davemuscle/10band_nixie/ltspice/AnalogStateVar_AC_DualSupply.asc

C1: cap; {CC}
C2: cap; {CC}
R1: res; {RR1}
R2: res; {RR2}
R3: res; {RR3}
R4: res; {RR}
R5: res; {RR}
R6: res; {RR6}
R7: res; {RR7}
R13: res; 10k
R14: res; 10k
U1: LT1632
U2: LT1632
U3: LT1632
V2: voltage; 2.5V
V3: voltage; -2.5V
V4: voltage; SINE(0 0.01 760); AC 1
Named nets: 0, V+, V-, Vbias, Vin, LP, BP, HP
.ac oct 24 20 20000
.param CC = 100n
.param RR1 = 10000
.param RR2 = 250
.param RR3 = 250
.param RR6 = 400k
.param RR = 2085
.param RR7 = 80k
