davemuscle/10band_nixie/ltspice/AnalogStateVar_AC_SingleSupply.asc

C1: cap; {CC}
C2: cap; {CC}
R1: res; {RR1}
R2: res; {RR2}
R3: res; {RR3}
R4: res; {RR_B1}
R5: res; {RR_B1}
R6: res; {RR7}
R7: res; {RR6}
R8: res; 10k
R9: res; 1k
U1: LT1632
U2: LT1632
U3: LT1632
U4: LT1632
V1: voltage; 2.5V
V2: voltage; 5V
V4: voltage; SINE(2.5V 0.1 760); AC 0.1
Named nets: 0, V+, Vin, V-, Vbias, Vgain, Vbp
.ac oct 24 20 20000
.param CC = 100n
.param RR1 = 10000
.param RR2 = 1k
.param RR3 = 1k
.param RR6 = 220k
.param RR_B1 = 2200
.param RR7 = 10k
;.tran 0 0.02 0.00 0.005
