davemuscle/10band_nixie/ltspice/ButterworthBandpass.asc

C1: cap; 100n
C2: cap; 100n
C3: cap; 100n
C4: cap; 100n
C5: cap; 100n
C6: cap; 100n
C7: cap; 100n
C8: cap; 100n
C9: cap; 100n
C10: cap; 100n
C11: cap; 100n
C12: cap; 100n
R1: res; 3.6k
R2: res; 2.5k
R3: res; 3.6k
R4: res; 500
R5: res; 300
R6: res; 300
R7: res; 500
R8: res; 4.3k
R9: res; 470
R10: res; 2.5k
R11: res; 3.3k
R12: res; 360
R13: res; 10k
R14: res; 10k
R15: res; 27k
R16: res; 22k
R17: res; 3k
R18: res; 330
R19: res; 2.2k
R20: res; 270
R21: res; 19k
R22: res; 15k
U1: LT1490
U2: LT1490
U3: LT1490
U4: LT1490
U5: LT1490
U6: LT1490
U7: LT1490
V1: voltage; -5V
V2: voltage; 5V
V4: voltage; SINE(2.5V 0.1 760); AC 0.1
Named nets: 0, V+, Vin, V-, Vbias
.ac oct 24 20 20000
;.tran 0 0.02 0.00 0.005
Lowpass is 440 Hz, Highpass is 630 Hz
Lowpass is 630 Hz, Highpass is 900 Hz (approx same Q as above)
