davemuscle/10band_nixie/ltspice/Chopper.asc

D1: diode; 1N914
D2: diode; 1N914
R1: res; 1k
V1: voltage; 1.8
V2: voltage; SINE(0 5 440)
Named nets: 0
.tran 0 0.01 0.00 0.005
