davemuscle/10band_nixie/ltspice/Doubler.asc

C1: polcap; 10µ
C2: polcap; 10µ
C3: polcap; 2.2µ
C4: polcap; 2.2µ
D1: diode; MURS120
D2: diode; MURS120
D3: diode; MURS120
D4: diode; MURS120
V1: voltage; PULSE(0 50 0 0 0 10us 20us)
V2: voltage; 50
Named nets: 0, Vin, Vdc
.tran 0 800u 0 1u
