davemuscle/10band_nixie/ltspice/FrontEnd.asc

C1: cap; 10µ
D1: diode
D2: diode
Q1: npn; 2N2222
Q2: npn; 2N2222
R1: res; {RR}
R2: res; {POT}
R3: res; {10.01k - POT}
R4: res; {POT}
R5: res; 500
R6: res; {RR}
R7: res; {RR}
R8: res; 500
R9: res; {RR}
R10: res; {RR}
R11: res; {RR}
R12: res; {RR}
R13: res; {RR}
R14: res; {RR}
R15: res; {2*RR}
R16: res; {2*RR}
R17: res; 1k
U1: LT1632
U2: LT1632
U3: LT1632
U4: LT1632
U5: LT1632
U6: LT1632
V1: voltage; 5V
V2: voltage; 2.5V
V3: voltage; SINE(0V 1 440 0 0 0 10)
Named nets: 0, V+, Vbias, Vin, Vpot, Vgain, Vatt
.tran 0 0.02 0.00 0.01
.param POT = 1
.param RR = 5k
