davemuscle/10band_nixie/ltspice/GaintoDB.asc

R1: res; 1k
R2: res; 1k
R3: res; 1k
R4: res; 1k
R5: res; 1k
R6: res; 1k
R7: res; 1k
R8: res; 1k
R9: res; 1k
R10: res; 1k
U1: LT1632
U2: LT1632
U3: LT1632
U4: LT1632
U5: LT1632
U6: LT1632
U7: LT1632
U8: LT1632
U9: LT1632
U10: LT1632
V1: voltage; 2.5
V2: voltage; 5
V3: voltage; 2.5V
V4: voltage; 2V
V5: voltage; 1.5V
V6: voltage; 1V
V7: voltage; 0.5V
V8: voltage; 0V
V9: voltage; 2.5V
V10: voltage; 3V
V11: voltage; 3.5V
V12: voltage; 4V
V13: voltage; 4.5V
Named nets: 0, Vbias, V+, Vgain
Potentiometer is 10K -> Vgain = 5V, gain = 6 dB
Potentiometer is 0K   -> Vgain = 0V, gain = -21 dB
.tran 0 10m 0 100u
