davemuscle/10band_nixie/ltspice/MFT.asc

C1: cap; {CC}
C2: cap; {CC}
C3: cap; {CC}
C4: cap; {CC}
R1: res; {RR3}
R2: res; {RR1}
R3: res; {RR2}
R4: res; {RR3}
R5: res; {RR1}
R6: res; {RR2}
U1: LT1632
U2: LT1632
V1: voltage; 5V
V2: voltage; 2.5V
V3: voltage; SINE(2.5V 100m 1.7k); AC 0.1
Named nets: 0, Vbias, V+, Vin
.param RR1 = 3905
.param RR2 = 7800
.param CC = 100n
.ac oct 20 20 20k
;.tran 0 0.025 0.00 0.05
.param RR3 = 240
