davemuscle/10band_nixie/ltspice/PeakDetect.asc

C1: cap; 10µ
C2: cap; 10µ
C3: cap; 1µ
C4: cap; 10µ
C5: cap; 10µ
C6: cap; 10µ
D1: diode; 1N4148
D2: diode; 1N4148
D3: diode; 1N4148
R1: res; 10k
R2: res; 100
R3: res; 10k
R4: res; 100
R5: res; 100k
R6: res; 10k
R7: res; 10k
R8: res; 10k
R9: res; 100
U1: LT1632
U2: LT1632
U3: LT1632
U4: LT1632
U5: LT1632
U6: LT1632
V1: voltage; 5V
V2: voltage; SINE(2.5V 0.5 120 0 0 0 20)
V3: voltage; -5V
V4: voltage; 2.5V
Named nets: 0, VIN, VCC, VSS, Vin, Vbias
.tran 0 1 0.00 0.005
