davemuscle/10band_nixie/ltspice/PeakDetectorForCompressor.asc

C1: cap; 10µ
C2: cap; 1µ
D1: diode; 1N914
D2: diode; 1N914
D3: diode; 1N914
Q1: npn; 2N2222
Q2: npn; 2N2222
R1: res; 10k
R2: res; 1k
R3: res; 100
R4: res; 620k
R5: res; 100
R6: res; 1k
U1: LT1632
U2: LT1632
V1: voltage; SINE(0 5 440)
V2: voltage; 5V
V3: voltage; 2.5V
Named nets: 0, Input, V+, Vbias
.tran 0 0.01 0.00 0.05
