davemuscle/10band_nixie/ltspice/SallenKeyButterworthBandpass.asc

C1: cap; 100n
C2: cap; 100n
C3: cap; 100n
C4: cap; 100n
R1: res; 1.1k
R2: res; 1.1k
R3: res; 2.2k
R4: res; 2.2k
U1: LT1490
U2: LT1490
U3: LT1490
V1: voltage; SINE(0 0.1 440); AC 0.1
V2: voltage; 5V
V3: voltage; -5V
Named nets: 0, Vin, 5V, -5V
.ac oct 50 20 20k
