davemuscle/10band_nixie/ltspice/SelfBoost.asc

C1: cap; 100µ
D1: diode; 1N914
L1: ind; 100µ
M1: nmos; IPB065N15N3
R1: res; 100
V1: voltage; 12V
V2: voltage; PULSE(0 5 0 0 0 90u 100u 800)
Named nets: 0, Vsw
.tran 0 0.05 0.00 0.01
