davemuscle/10band_nixie/ltspice/SimpleFrontEnd.asc

C1: cap; 10µ
D1: diode; 1N914
D2: diode; 1N914
R1: res; 1k
V1: voltage; 2.5V
V2: voltage; 5V
V3: voltage; SINE(0 2 440)
V4: voltage; 0.7
V5: voltage; 0.7
Named nets: 0, Vbias, Vin, 5V
.tran 0 10m 0 1u
