davemuscle/10band_nixie/ltspice/SimpleStateVar.asc

C3: cap; {CC}
C4: cap; {CC}
R1: res; 1k
R2: res; 1k
R5: res; {RG}
R6: res; {RQ}
R7: res; {RR4}
R8: res; {R12}
R9: res; {R12}
R10: res; {RR}
R11: res; {RR}
U4: LT1632
U5: LT1632
U6: LT1632
V1: voltage; 5V
V3: voltage; SINE(2.5V 500m 1.7k); AC 0.1
Named nets: 0, V+, Vin, Vbias
.param R12 = 1k
.param RG = 470
.param RR = 800
.param CC = 100n
.ac oct 20 20 20k
;.tran 0 0.025 0.00 0.05
.param RR4 = 47k
.param RQ = 4.3k
