davemuscle/10band_nixie/ltspice/TubeDriver.asc

Q1: npn; 2N5550
Q3: npn; 2N5550
Q4: npn; 2N5550
R1: res; 10k
R5: res; 200
R6: res; 300
V1: voltage; 5V
V2: voltage; SINE(0 2 120 0 0 0 10)
V3: voltage; 2.5V
V4: voltage; 140V
V5: voltage; SINE(2.5V 2 440 0 0 0 10)
V6: voltage; PULSE(0 5 0 0 0 0.0083 0.0166 10)
V7: voltage; 2.5V
Named nets: 0, Vin, VCC, Vbias, Vtube, Vin_b, SQ
.tran 0 0.05 0.00 0.01
