davemuscle/10band_nixie/ltspice/TubeDriverDemo.asc

NixieTube: diode; IN-9
Q1: npn
R1: res
R2: res
Named nets: 0
Vb
Ve
~150V
Ve = Vb - 0.7 (typical)
Itube = Ve / R1
IN-9 operation: 0-10 mA
IN-9 burn-in: 20 mA+
Realistic operation of the tube requires Vb to be pulsed
when using an SMPS. Not required if connecting to AC power
